eastcoalmine/Labornetzgeraet/Bilder/IMG_20260315_183434.jpg

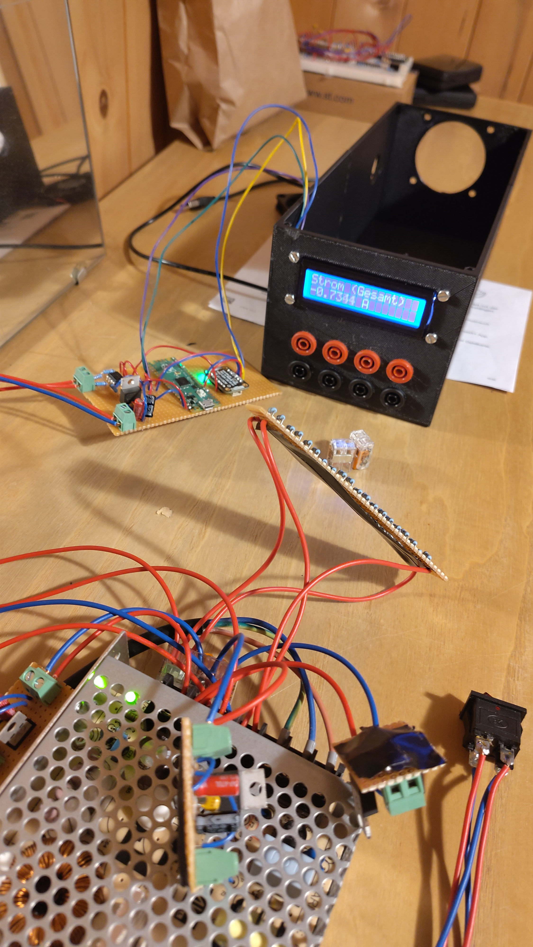
Bilder/IMG_20260315_183434.jpg
