eastcoalmine/Labornetzgeraet/Bilder/IMG_20260316_195358.jpg

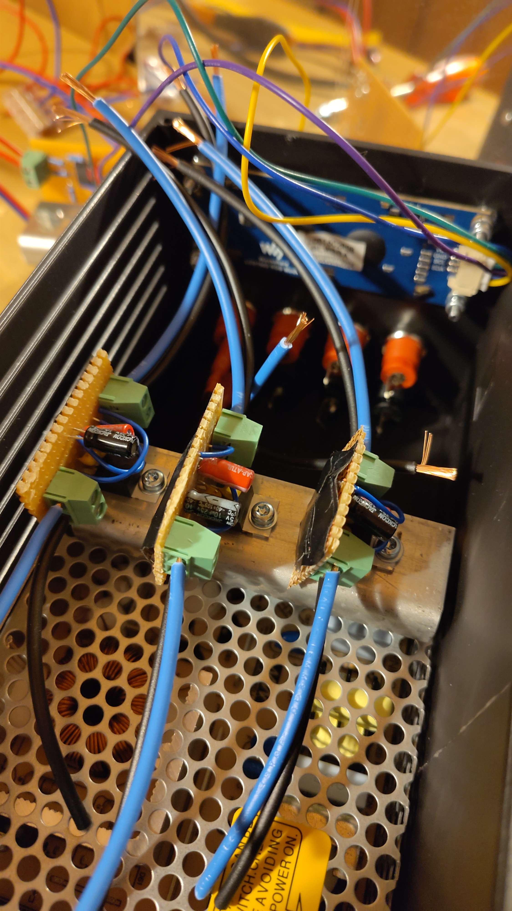
Bilder/IMG_20260316_195358.jpg
