eastcoalmine/Labornetzgeraet/Bilder/IMG_20260316_201155.jpg

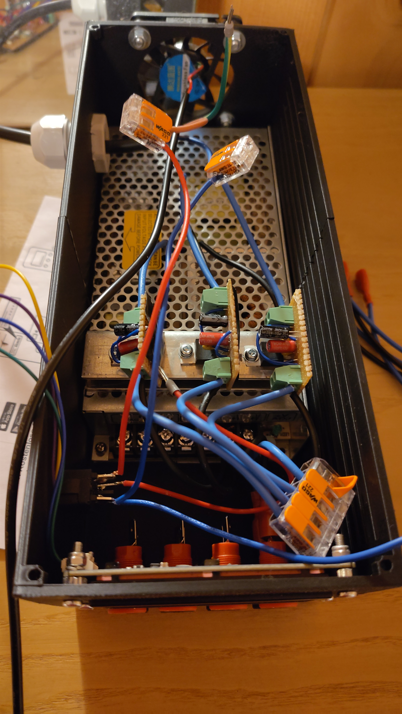
Bilder/IMG_20260316_201155.jpg
