eastcoalmine/Labornetzgeraet/Bilder/IMG_20260317_183655.jpg

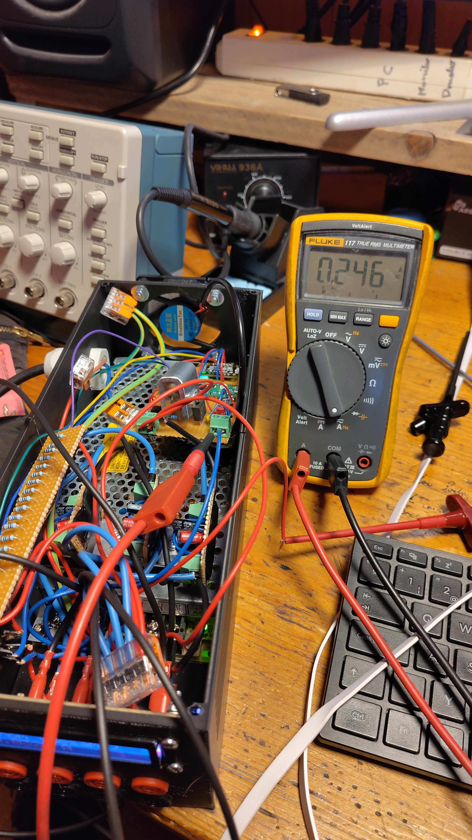
Bilder/IMG_20260317_183655.jpg
